Sillybutts/SkewerCrossbow/STLs/SkewBow v2/1WindowFlange.stl

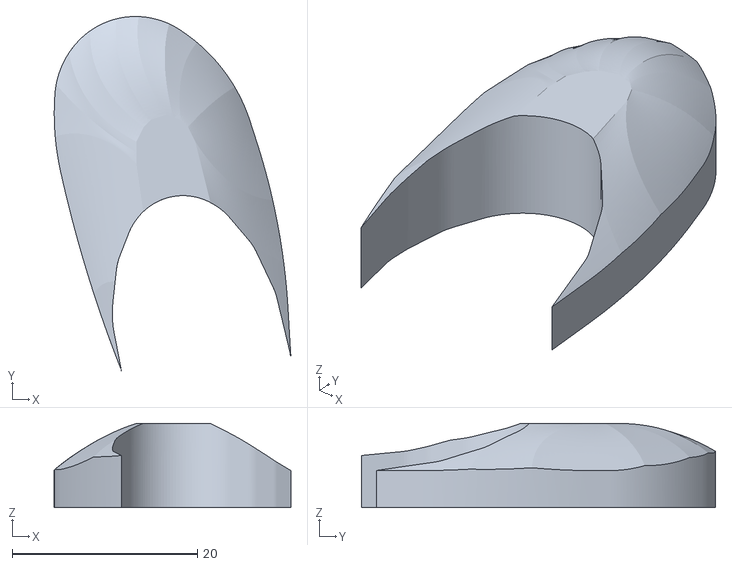
[picture p27: CAD file, 2021-09-28]
STLs/SkewBow v2/1WindowFlange.stl
25.5 x 38.2 x 9.08
