Sillybutts/SkewerCrossbow/STLs/SkewBow v2/1Grip.stl

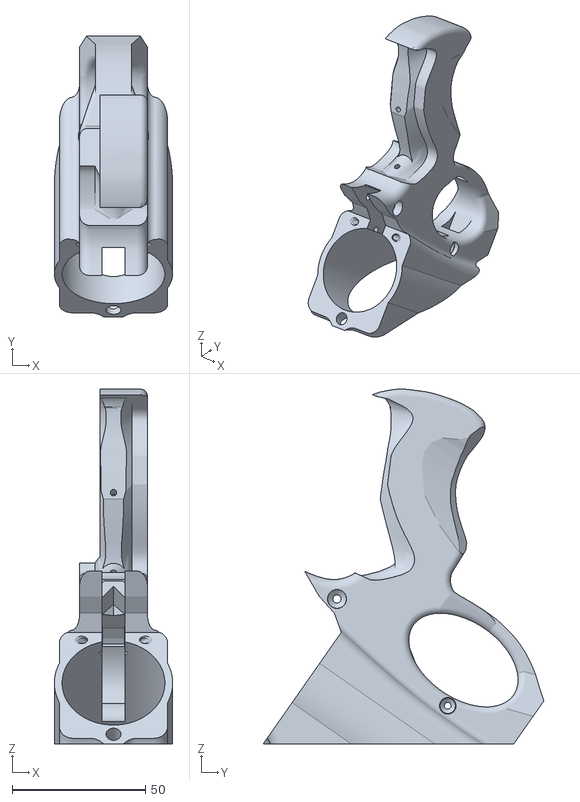
[picture p28: CAD file, 2021-09-28]
STLs/SkewBow v2/1Grip.stl
44.5 x 105.4 x 133.3
