Sillybutts/SkewerCrossbow/STLs/SkewBow v2/Trigger.stl

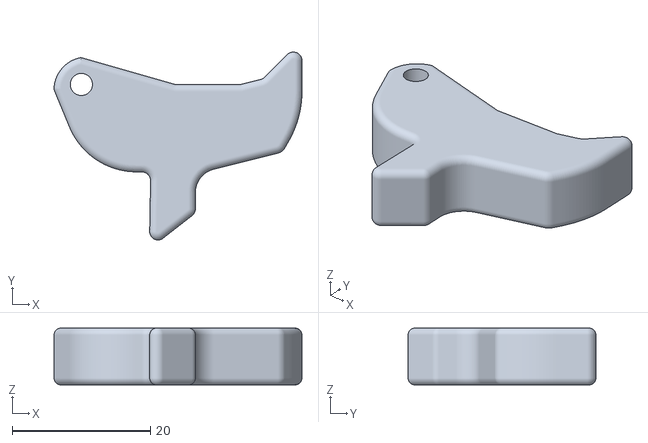
[picture p29: CAD file, 2021-09-28]
STLs/SkewBow v2/Trigger.stl
35.9 x 27.2 x 8.22
