Sillybutts/SkewerCrossbow/STLs/SkewBow v2/Foregrip1.stl

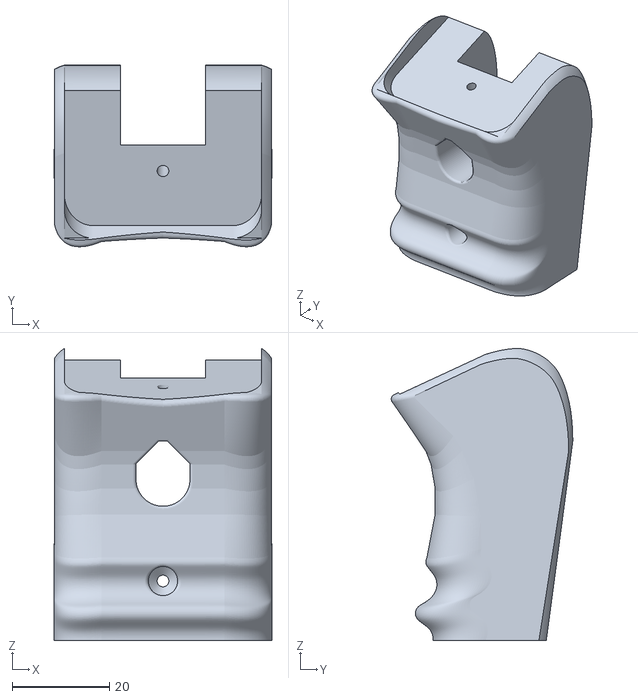
[picture p30: CAD file, 2021-09-28]
STLs/SkewBow v2/Foregrip1.stl
44.8 x 37.4 x 60.1
