Sillybutts/SkewerCrossbow/STLs/SkewBow v2/Scope.stl

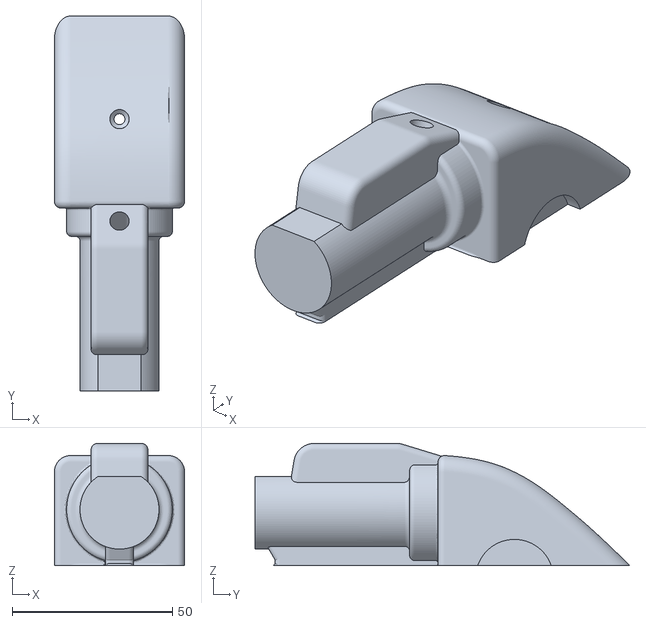
[picture p31: CAD file, 2021-09-28]
STLs/SkewBow v2/Scope.stl
40.6 x 117.0 x 38.1
