Sillybutts/SkewerCrossbow/STLs/SkewBow v2/MagRelease.stl

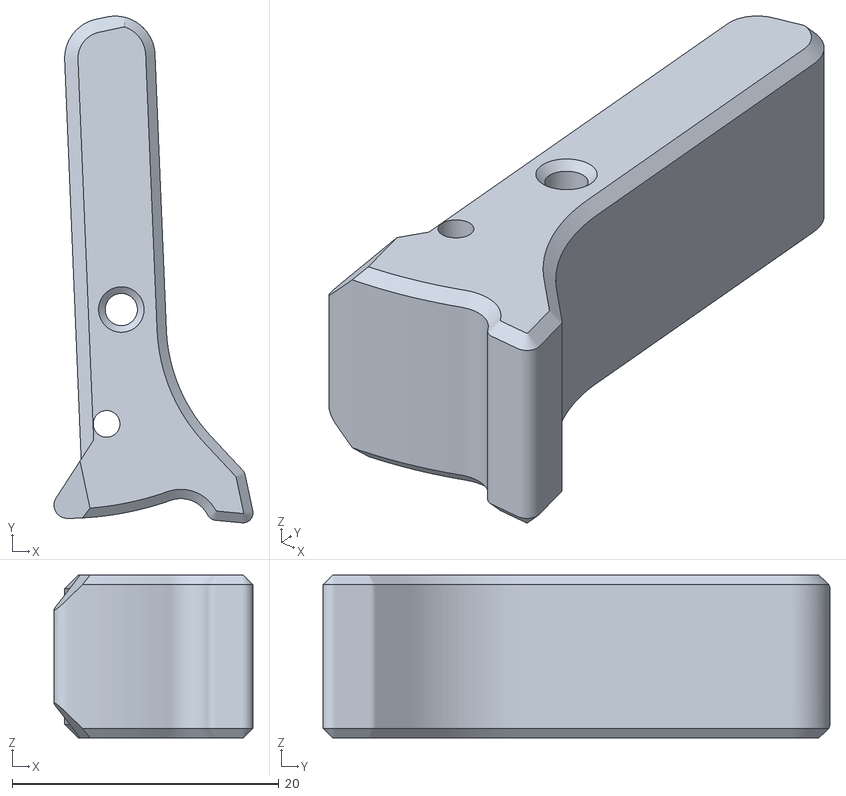
[picture p32: CAD file, 2021-09-28]
STLs/SkewBow v2/MagRelease.stl
14.9 x 38.0 x 12.2
