Sillybutts/SkewerCrossbow/STLs/SkewBow v2/Collet.stl

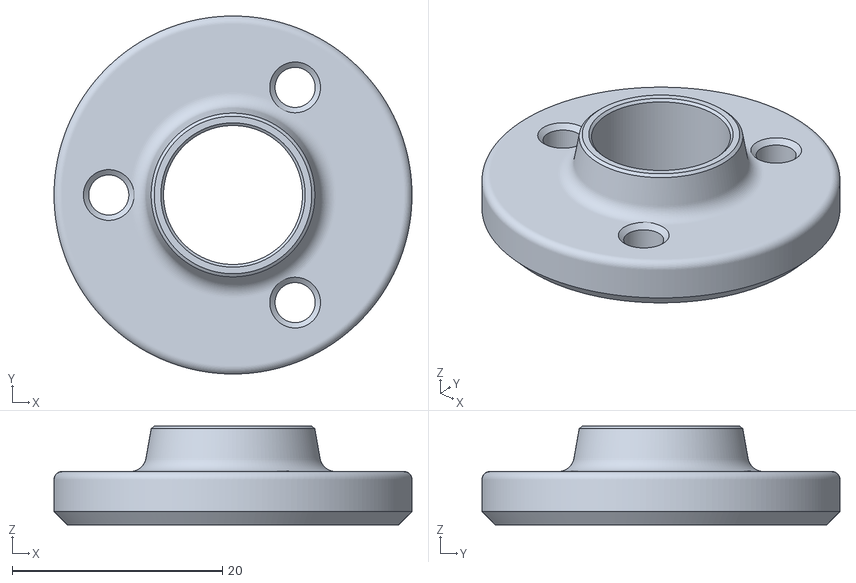
[picture p33: CAD file, 2021-09-28]
STLs/SkewBow v2/Collet.stl
34.0 x 34.0 x 9.40
