Sillybutts/SkewerCrossbow/STLs/SkewBow v2/Front1Tip.stl

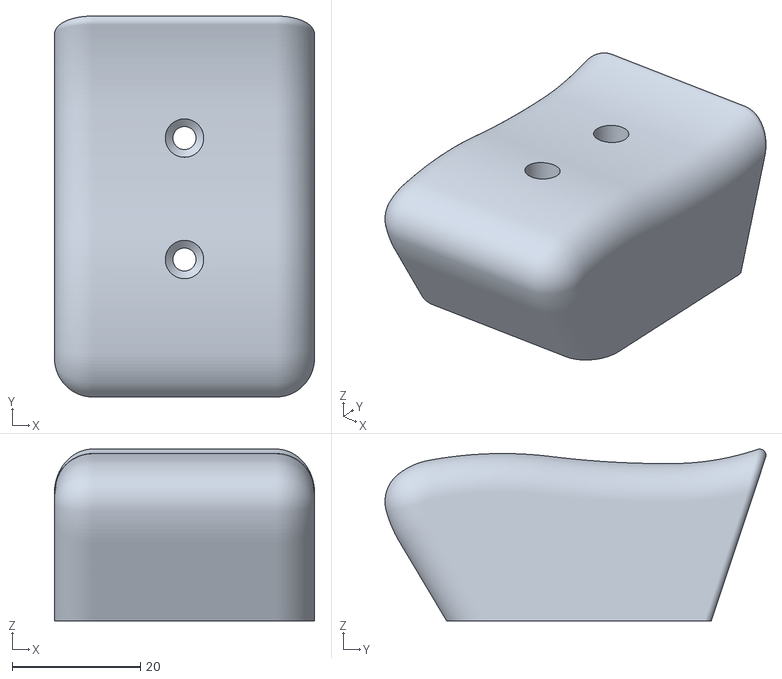
[picture p34: CAD file, 2021-09-28]
STLs/SkewBow v2/Front1Tip.stl
40.6 x 59.5 x 26.9
