Sillybutts/SkewerCrossbow/STLs/SkewBow v2/ScopePeg.stl

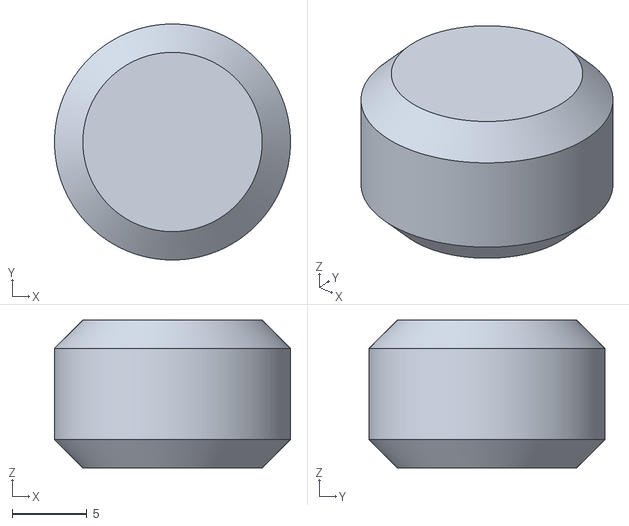
[picture p35: CAD file, 2021-09-28]
STLs/SkewBow v2/ScopePeg.stl
15.8 x 15.8 x 9.90
