Sillybutts/SkewerCrossbow/STLs/SkewBow v2/2Grip.stl

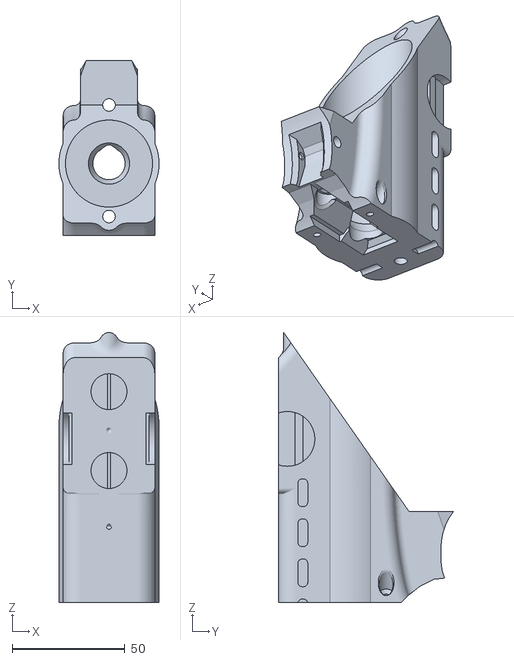
[picture p36: CAD file, 2021-09-28]
STLs/SkewBow v2/2Grip.stl
44.5 x 77.7 x 119.8
