Sillybutts/SkewerCrossbow/STLs/SkewBow v2/2Stock.stl

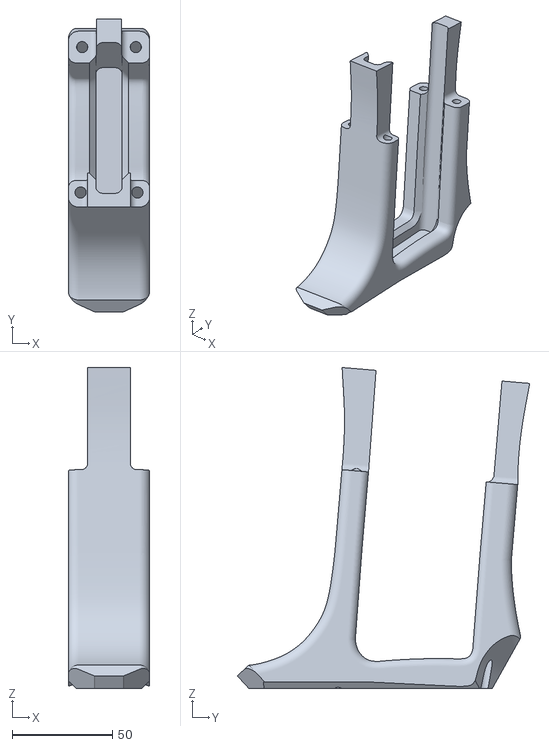
[picture p37: CAD file, 2021-09-28]
STLs/SkewBow v2/2Stock.stl
40.6 x 145.9 x 160.1
