Sillybutts/SkewerCrossbow/STLs/SkewBow v2/3Grip.stl

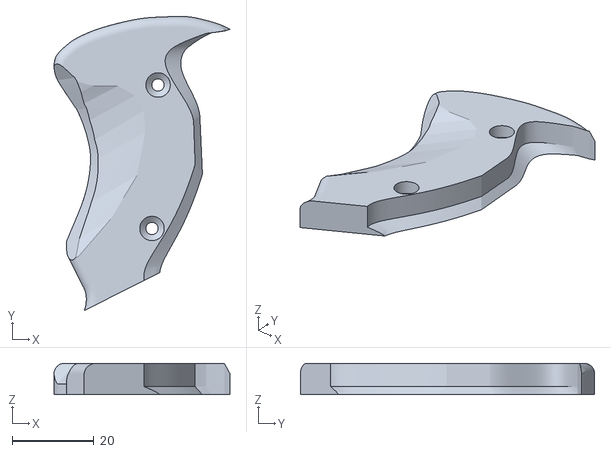
[picture p38: CAD file, 2021-09-28]
STLs/SkewBow v2/3Grip.stl
43.1 x 72.1 x 7.70
