Sillybutts/SkewerCrossbow/STLs/SkewBow v2/Sealer.stl

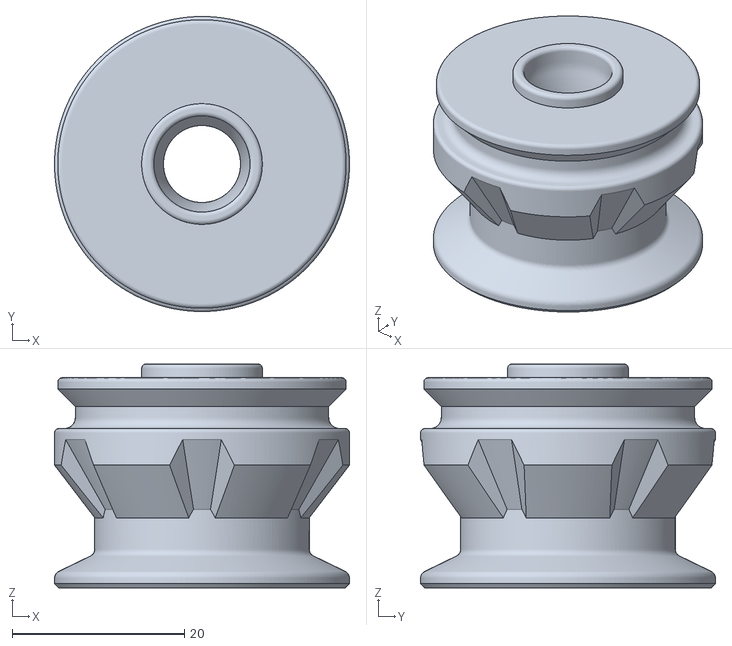
[picture p39: CAD file, 2021-09-28]
STLs/SkewBow v2/Sealer.stl
34.3 x 34.3 x 26.0
